MKme/Urban-Kitchen-Garden/Pics/2498291438060424755.jpg

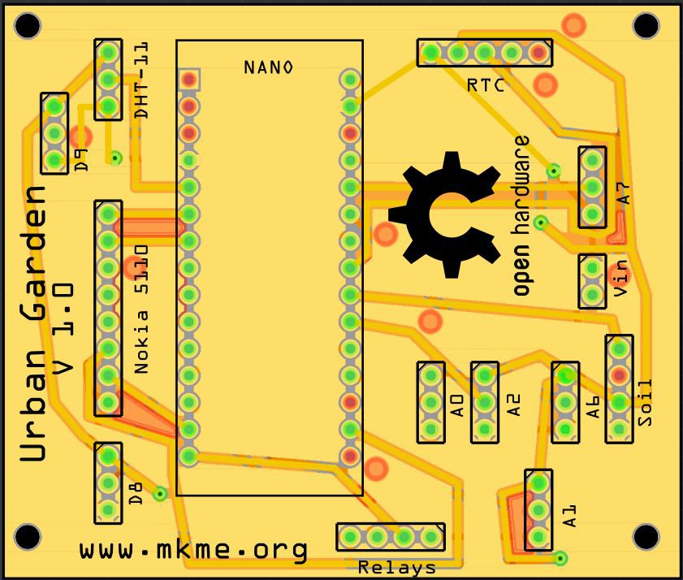
Pics/2498291438060424755.jpg
