MKme/Urban-Kitchen-Garden/Pics/263291438139597983.jpg

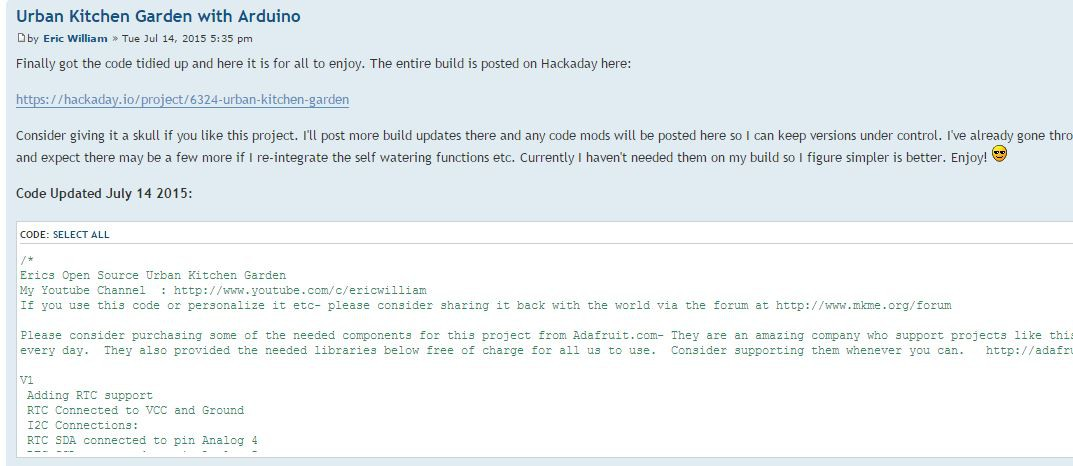
Pics/263291438139597983.jpg
