MKme/Urban-Kitchen-Garden/Pics/3371011438132859491.jpg

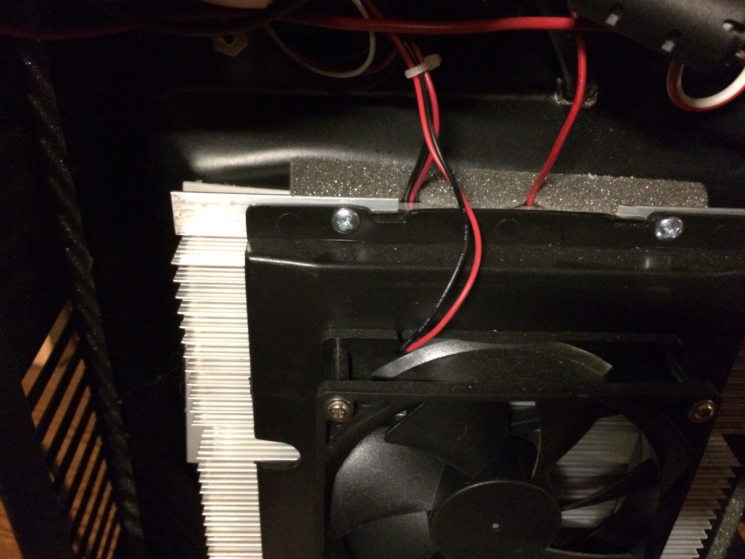
Pics/3371011438132859491.jpg
