MKme/Urban-Kitchen-Garden/Pics/3645261434434117013.jpg

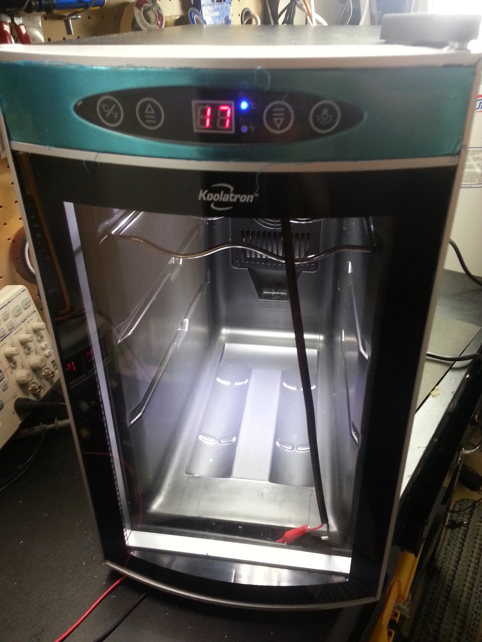
Pics/3645261434434117013.jpg
