MKme/Urban-Kitchen-Garden/Pics/4220201440124502944.jpg

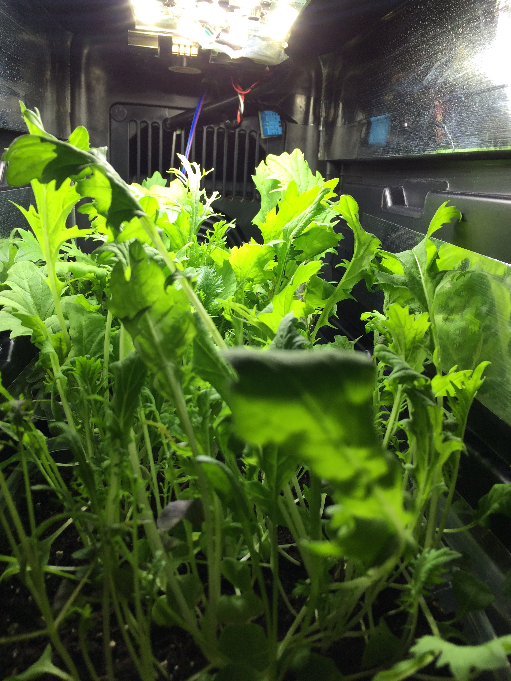
Pics/4220201440124502944.jpg
