MKme/Urban-Kitchen-Garden/Pics/4507771434562849108.jpg

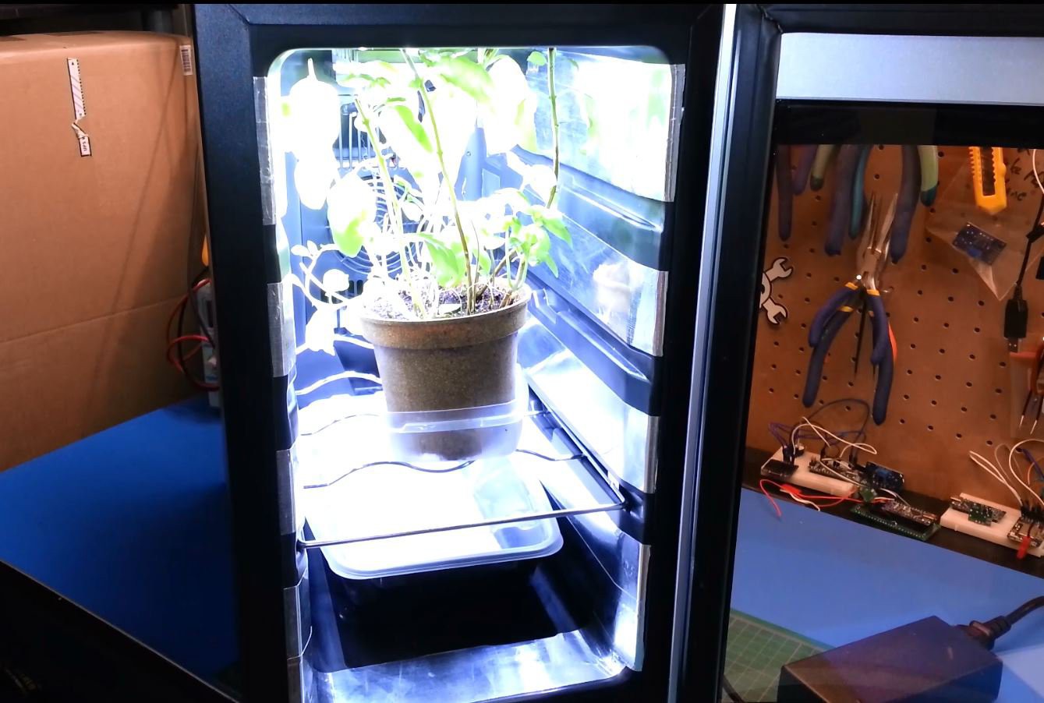
Pics/4507771434562849108.jpg
