MKme/Urban-Kitchen-Garden/Pics/4579501439817343015.jpg

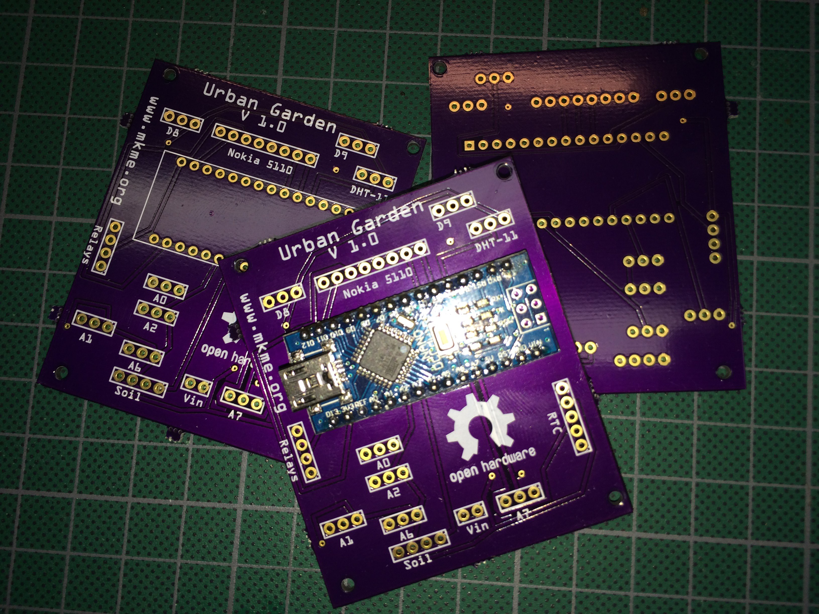
Pics/4579501439817343015.jpg
