MKme/Urban-Kitchen-Garden/Pics/4878191438060589979.jpg

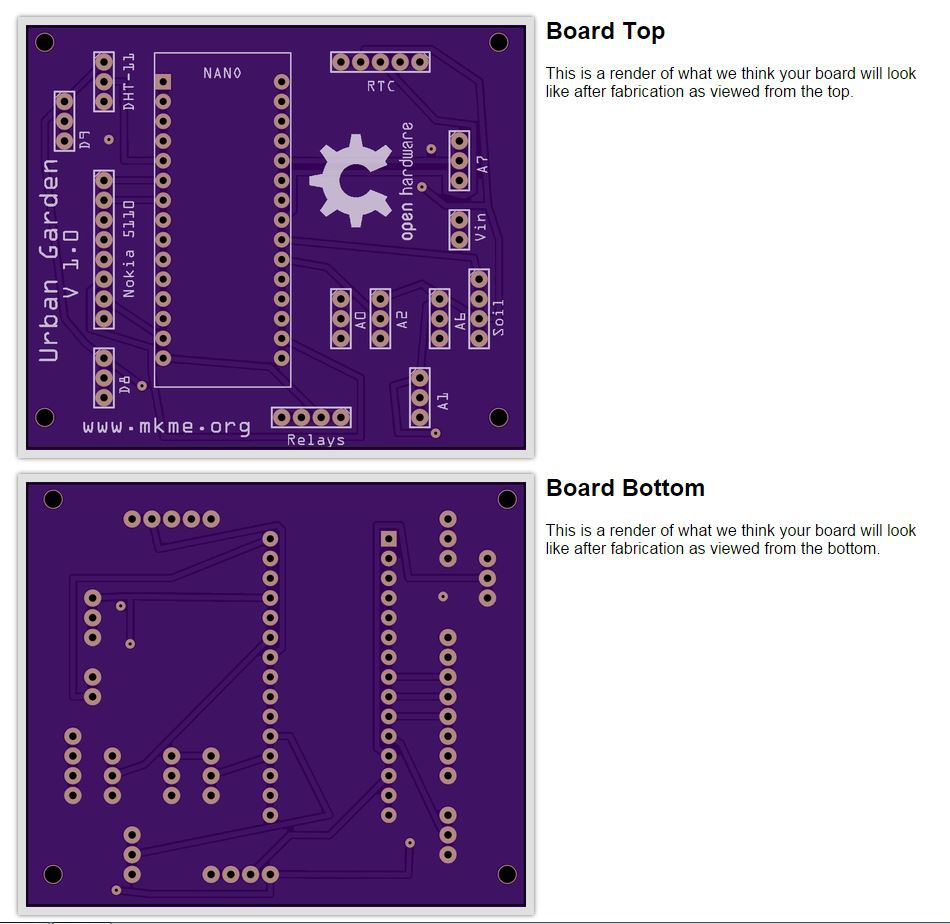
Pics/4878191438060589979.jpg
