MKme/Urban-Kitchen-Garden/Pics/5045911439003618221.jpg

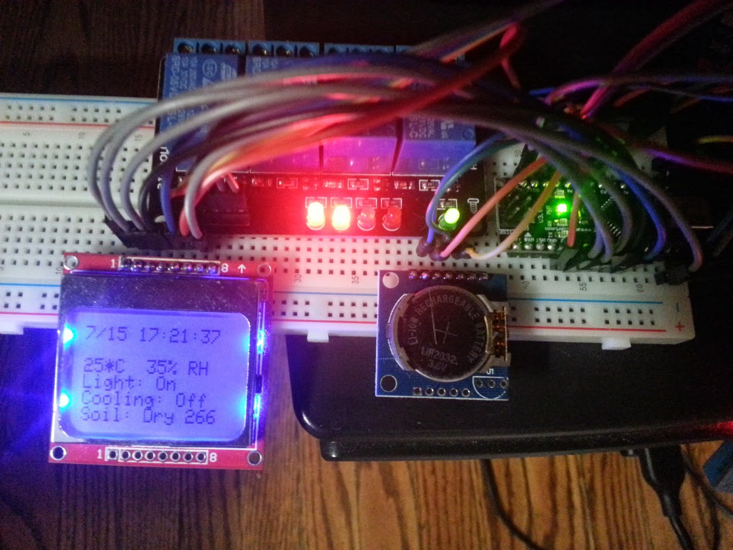
Pics/5045911439003618221.jpg
