MKme/Urban-Kitchen-Garden/Pics/5175641440126465656.jpg

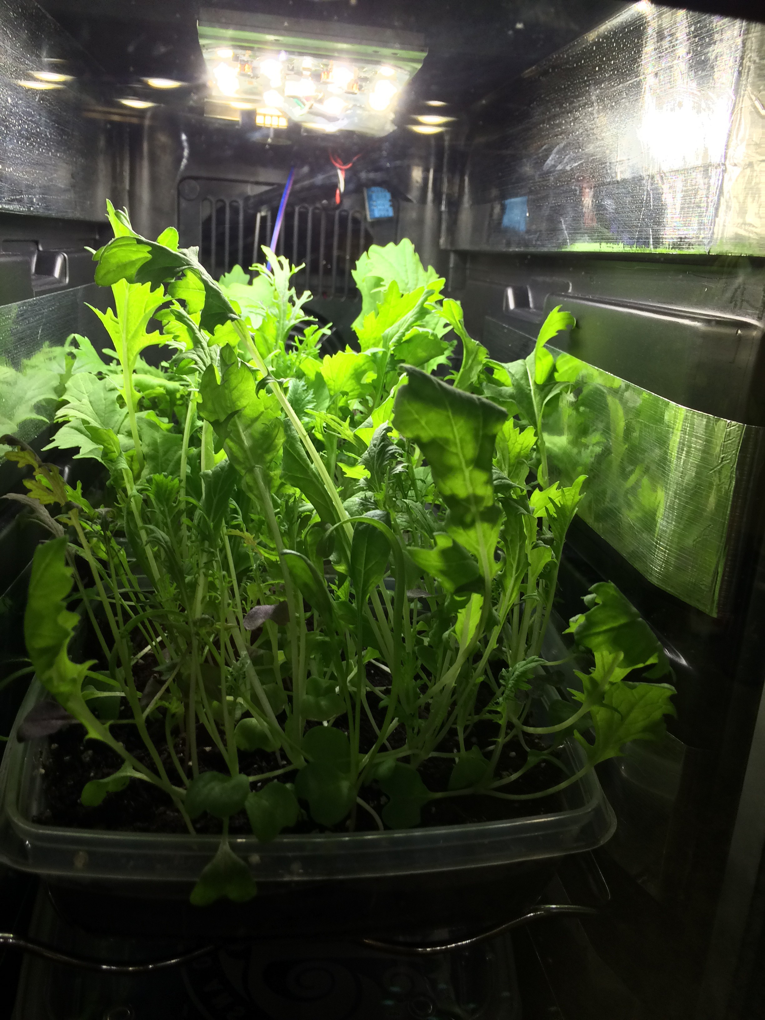
Pics/5175641440126465656.jpg
