MKme/Urban-Kitchen-Garden/Pics/7852841434433913665.jpg

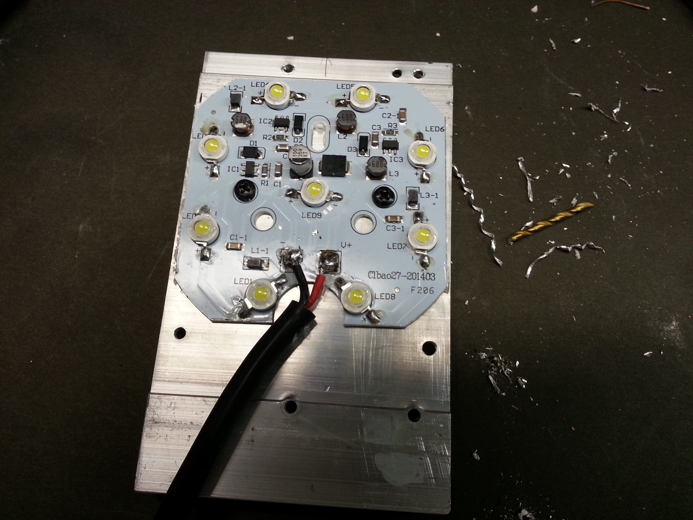
Pics/7852841434433913665.jpg
