MKme/Urban-Kitchen-Garden/Pics/8132821434434019283.jpg

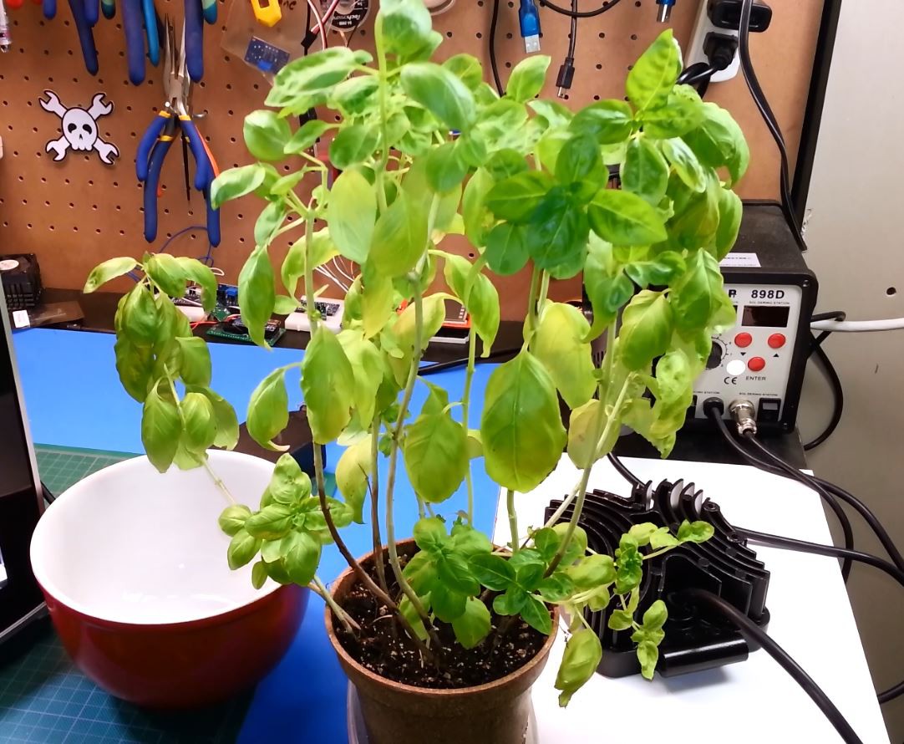
Pics/8132821434434019283.jpg
