MKme/Urban-Kitchen-Garden/Pics/9958561434424298217.jpg

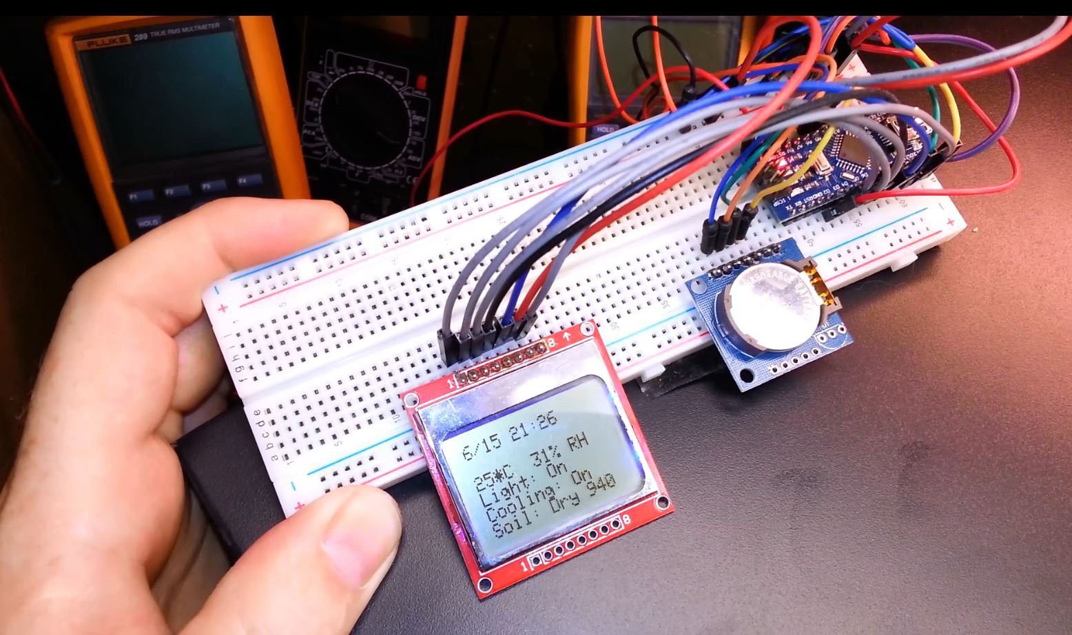
Pics/9958561434424298217.jpg
